arithmaldor/HD15-to-SCART/Photos/20190723_003617.jpg

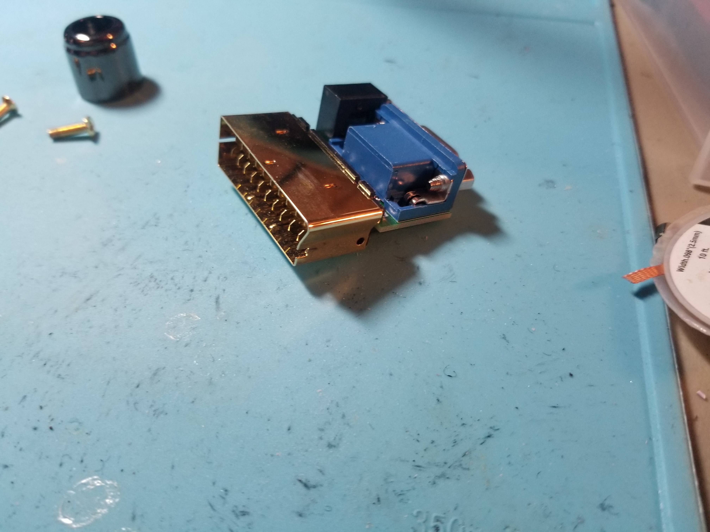
Photos/20190723_003617.jpg
